MacFlieger/Besucherzaehler/Schaltung/KiCad/Besucherzaehler.kicad_sch

## KiCad design Schaltung/KiCad/Besucherzaehler.kicad_sch (2022-08-24, an earlier design)

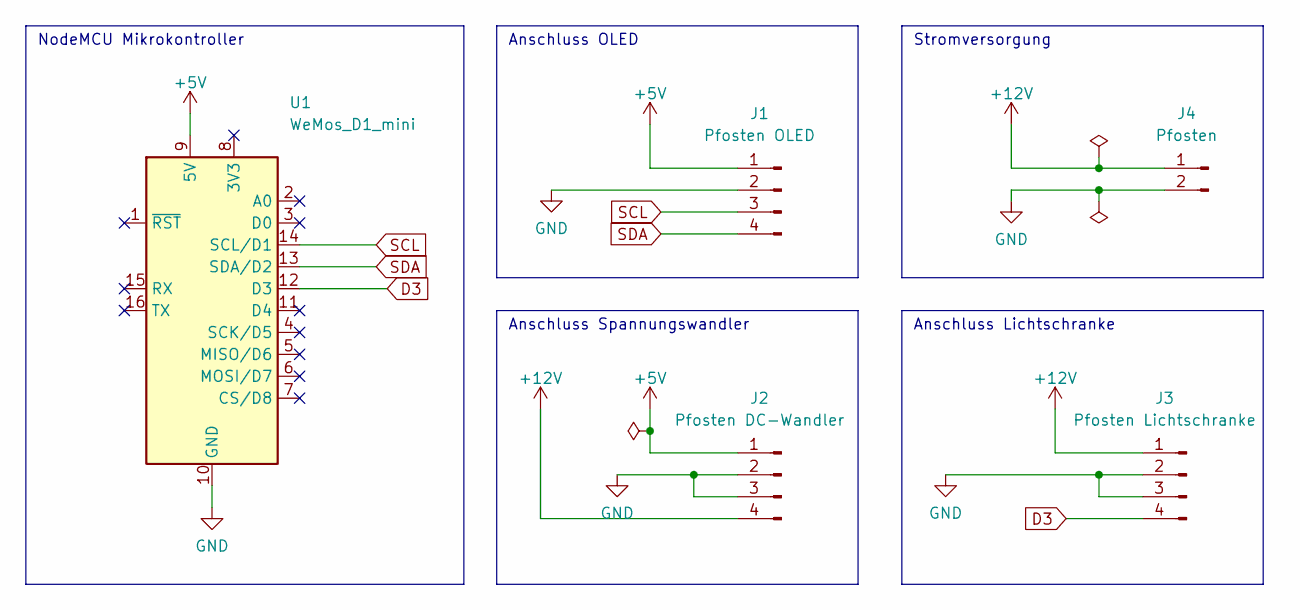
[picture p5: schematic Besucherzaehler.kicad_sch]

Parts:
J1: Pfosten OLED
J2: Pfosten DC-Wandler
J3: Pfosten Lichtschranke
J4: Pfosten
U1: WeMos_D1_mini; WEMOS_D1_mini_light

Connections:
+5V: J1.1, J2.1, U1.9 (5V)
+12V: J2.4, J3.1, J4.1
D3: J3.4, U1.12 (D3)
GND: J1.2, J2.2, J2.3, J3.2, J3.3, J4.2, U1.10 (GND)
SCL: J1.3, U1.14 (SCL/D1)
SDA: J1.4, U1.13 (SDA/D2)

Notes on the sheet:
NodeMCU Mikrokontroller
Anschluss Spannungswandler
Stromversorgung
Anschluss OLED
Anschluss Lichtschranke
